mosschief/robo_toy/docs/phone.png

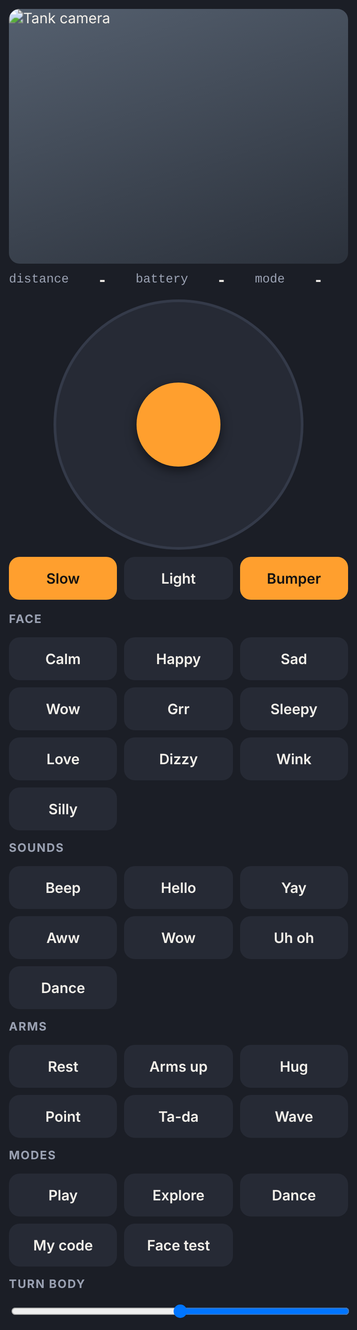
docs/phone.png
