mosschief/robo_toy/hardware/renders/tank_exploded.png

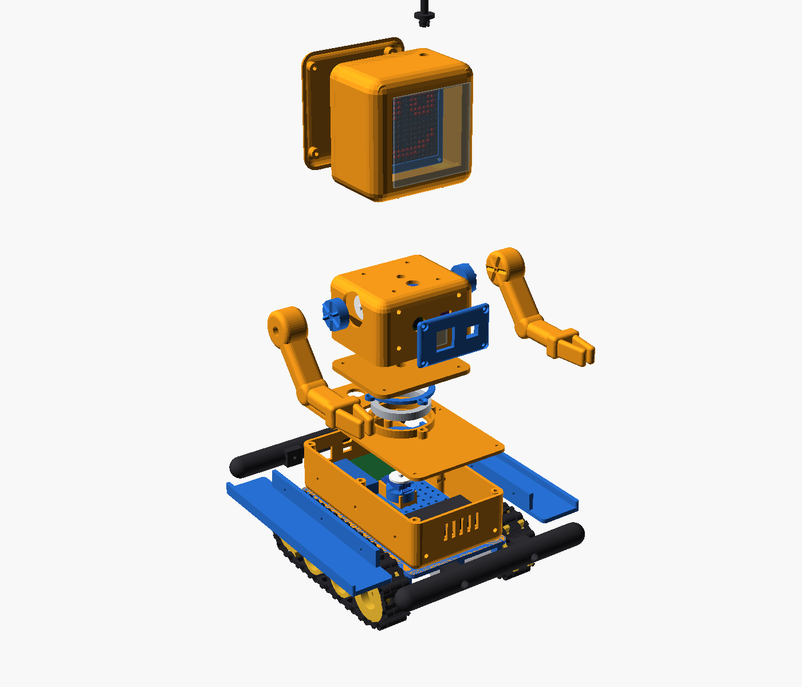
hardware/renders/tank_exploded.png
