mosschief/robo_toy/hardware/stl/chest_guard.stl

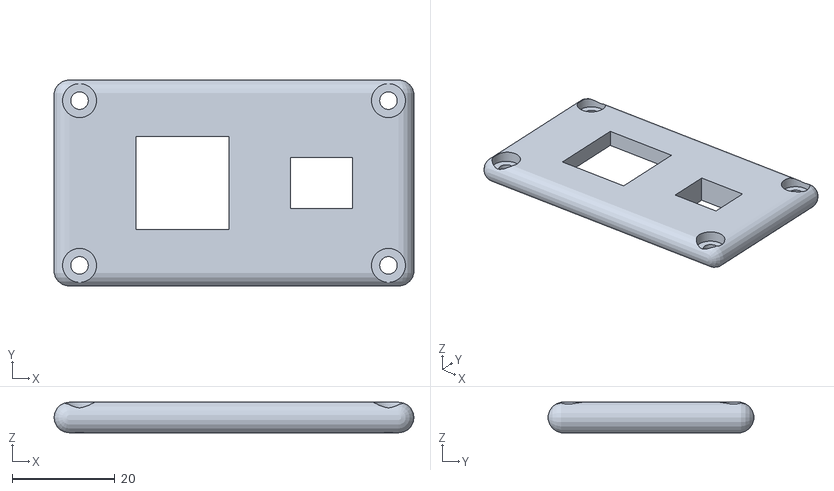
[picture p29: CAD file, 2026-10-07]
hardware/stl/chest_guard.stl
69.9 x 39.9 x 5.93
