mosschief/robo_toy/hardware/stl/track_link.stl

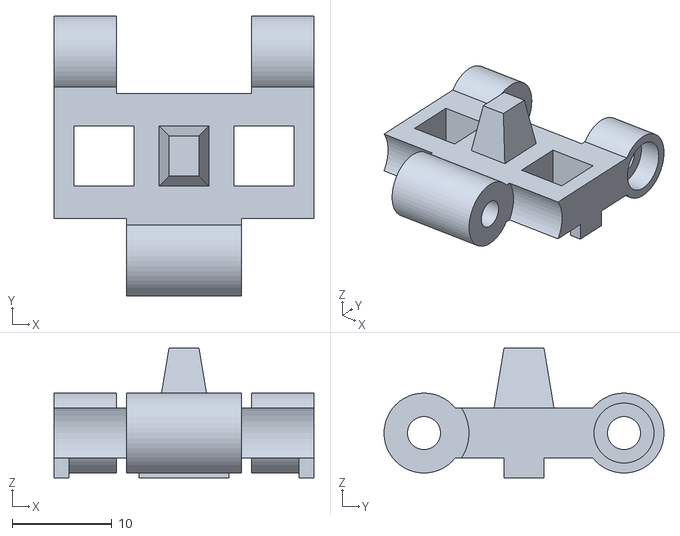
[picture p30: CAD file, 2026-10-07]
hardware/stl/track_link.stl
26.0 x 28.0 x 13.0
