mosschief/robo_toy/hardware/stl/bearing_cap.stl

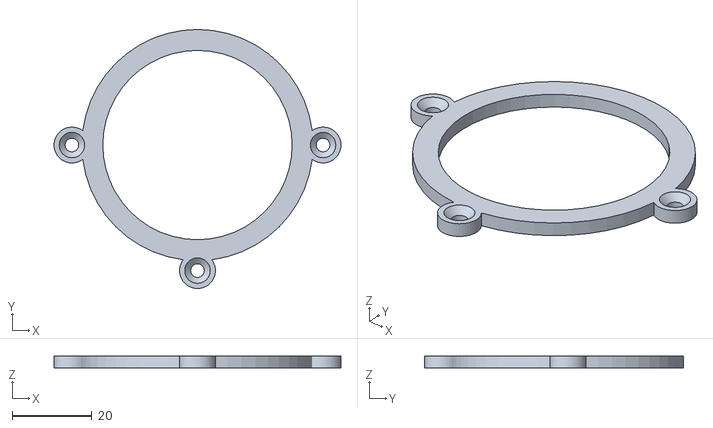
[picture p31: CAD file, 2026-10-07]
hardware/stl/bearing_cap.stl
72.0 x 65.0 x 3.00
