mosschief/robo_toy/hardware/stl/face_carrier.stl

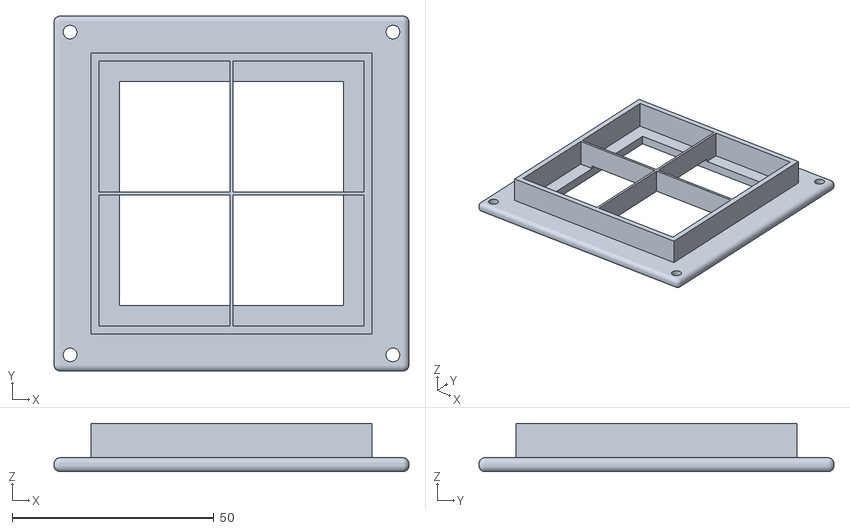
[picture p32: CAD file, 2026-10-07]
hardware/stl/face_carrier.stl
88.0 x 88.0 x 12.0
