mosschief/robo_toy/hardware/stl/lower_body.stl

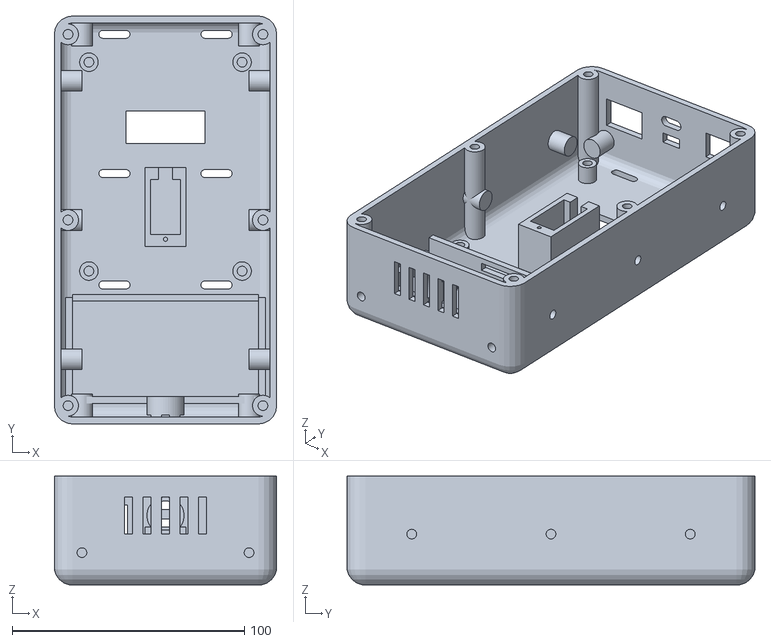
[picture p33: CAD file, 2026-10-07]
hardware/stl/lower_body.stl
95.8 x 175.8 x 46.9
