mosschief/robo_toy/hardware/stl/wheel_spacer.stl

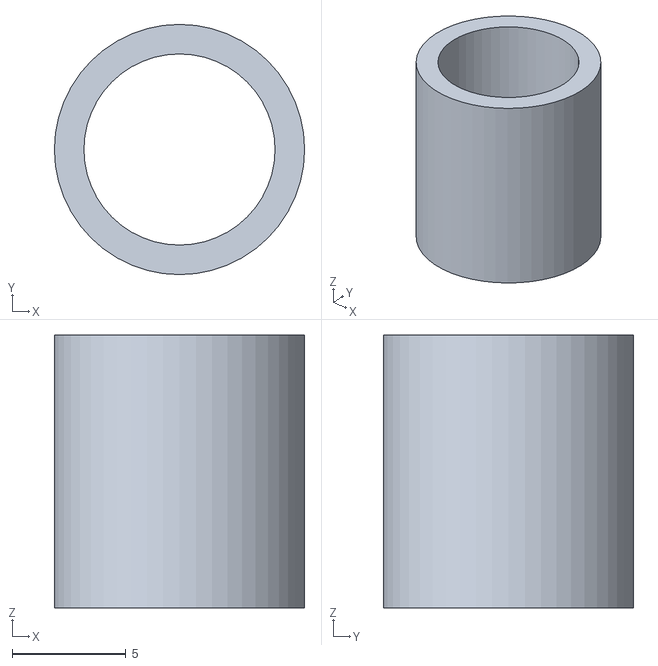
[picture p34: CAD file, 2026-10-07]
hardware/stl/wheel_spacer.stl
11.0 x 11.0 x 12.0
