mosschief/robo_toy/hardware/stl/fender.stl

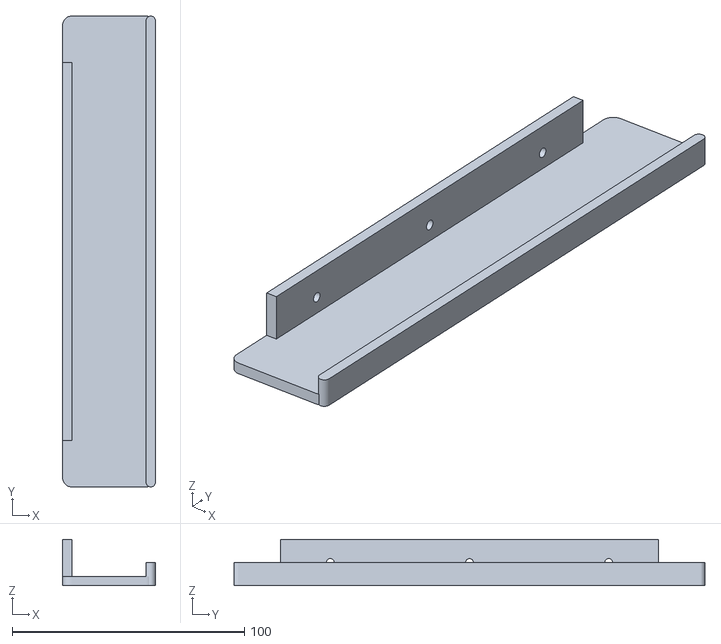
[picture p35: CAD file, 2026-10-07]
hardware/stl/fender.stl
40.0 x 203.0 x 20.0
