mosschief/robo_toy/hardware/stl/bumper.stl

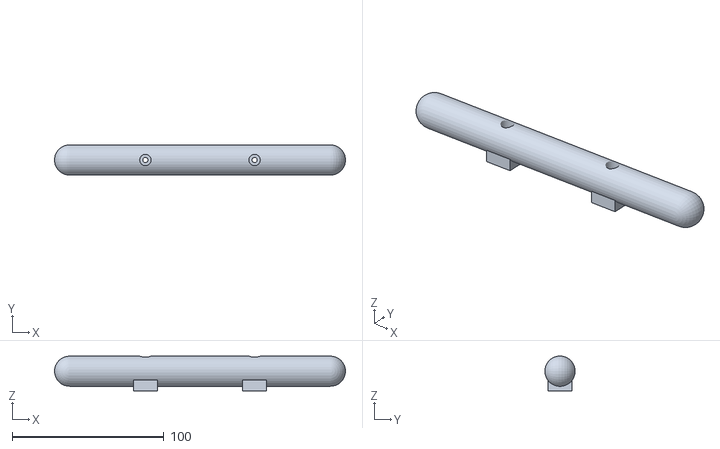
[picture p36: CAD file, 2026-10-07]
hardware/stl/bumper.stl
191.9 x 19.9 x 23.0
