mosschief/robo_toy/hardware/stl/tray.stl

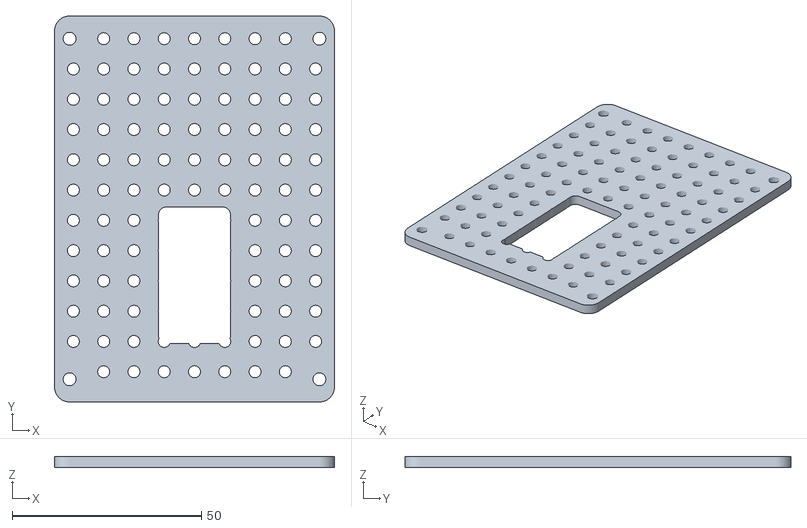
[picture p37: CAD file, 2026-10-07]
hardware/stl/tray.stl
74.0 x 102.0 x 3.00
